rolohaun/Bijou/Y/Y_Right_M3.stl

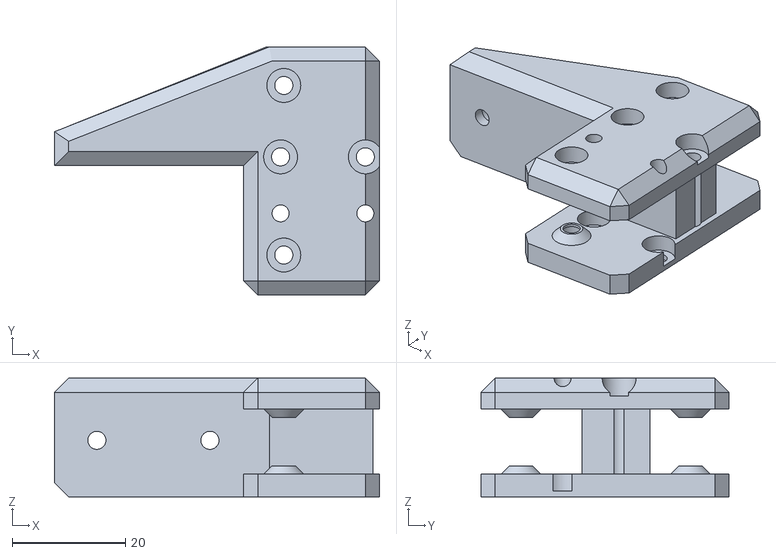
[picture p16: CAD file, 2022-08-20]
Y/Y_Right_M3.stl
57.5 x 43.9 x 21.0
