rolohaun/Bijou/Frame + Motor Mounts/Right_Motor_Mount.stl

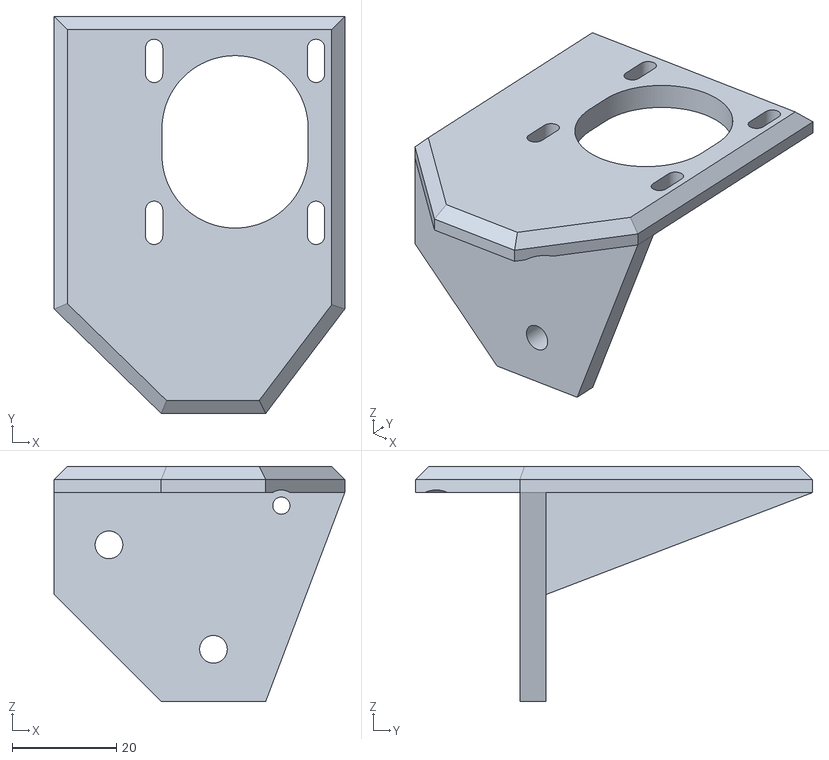
[picture p17: CAD file, 2022-09-24]
Frame + Motor Mounts/Right_Motor_Mount.stl
55.6 x 76.0 x 45.0
