rolohaun/Bijou/Klicky/KlickyProbe_v2.stl

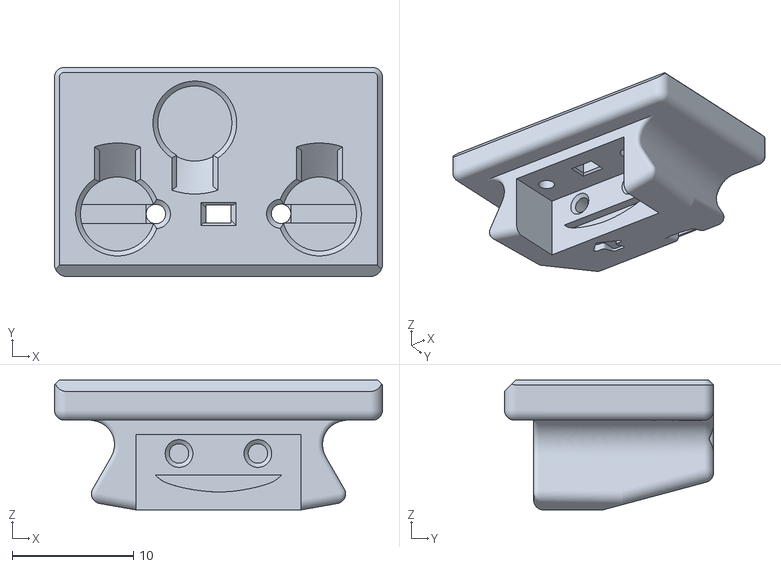
[picture p18: CAD file, 2022-08-20]
Klicky/KlickyProbe_v2.stl
27.0 x 17.2 x 10.7
