rolohaun/Bijou/Z Belted/2 X Z_Idler_Mount.stl

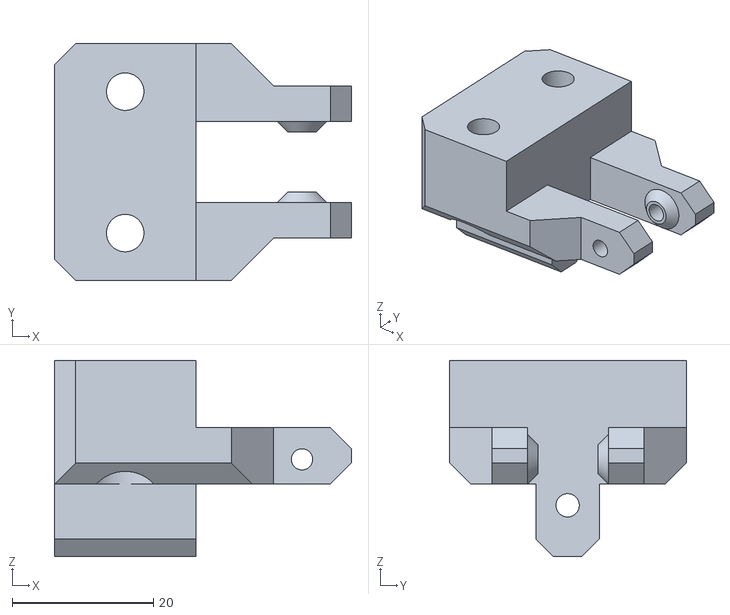
[picture p19: CAD file, 2022-09-28]
Z Belted/2 X Z_Idler_Mount.stl
42.0 x 33.5 x 27.8
