rolohaun/Bijou/Frame + Motor Mounts/Guide_Tube_Mount.stl

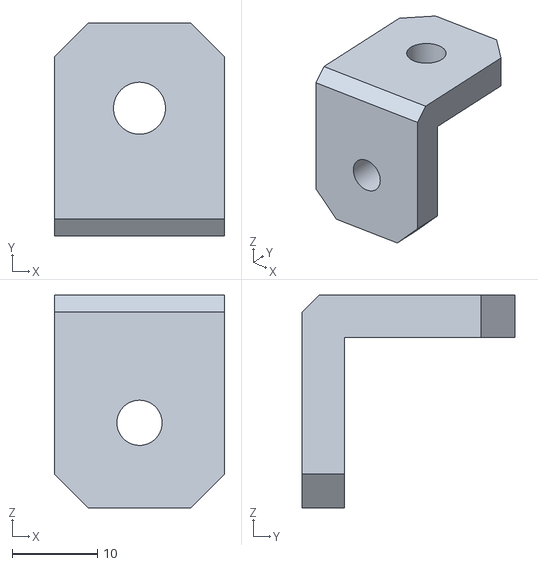
[picture p20: CAD file, 2022-08-24]
Frame + Motor Mounts/Guide_Tube_Mount.stl
20.0 x 25.0 x 25.0
