rolohaun/Bijou/Frame + Motor Mounts/Left_Idler_Mount_M3.stl

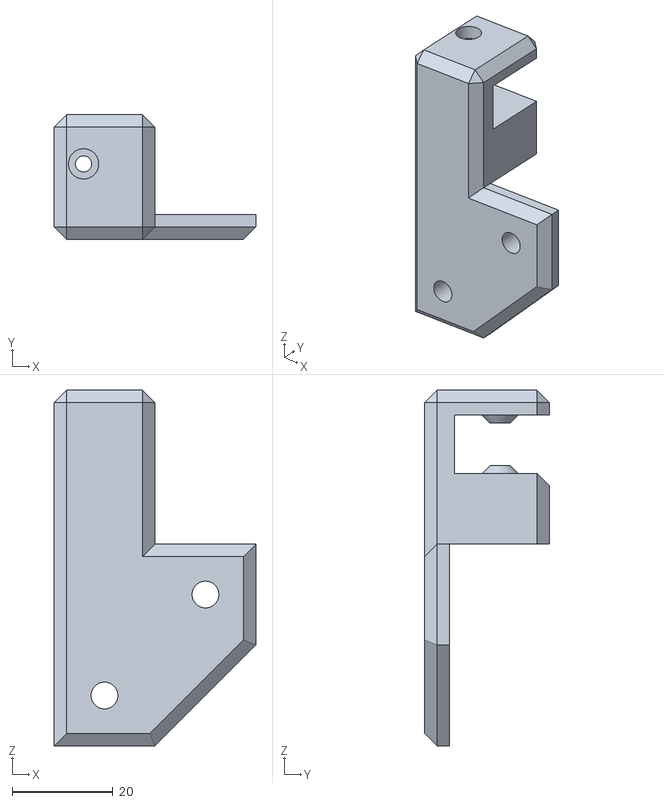
[picture p21: CAD file, 2022-08-20]
Frame + Motor Mounts/Left_Idler_Mount_M3.stl
40.0 x 24.8 x 70.5
